bmomofoma/ESP32-Sensor-Interface/assets/Layers.png

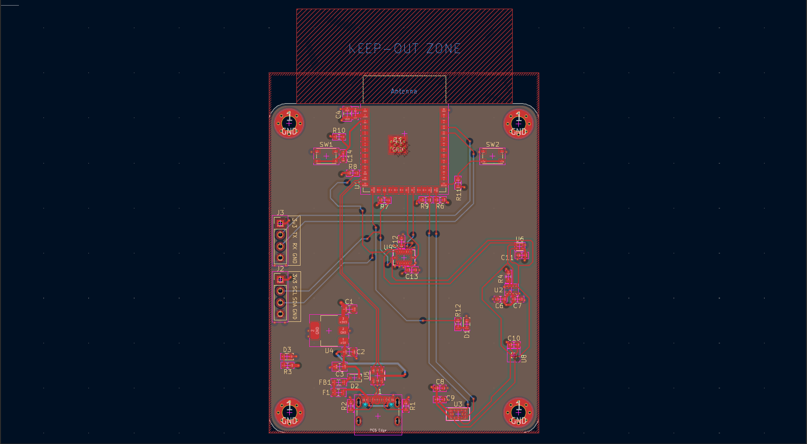
assets/Layers.png
